lcdporto/warehouse-locator/hardware/warehouse-locator.kicad_sch

## KiCad design hardware/warehouse-locator.kicad_sch (2023-01-04, an earlier design)

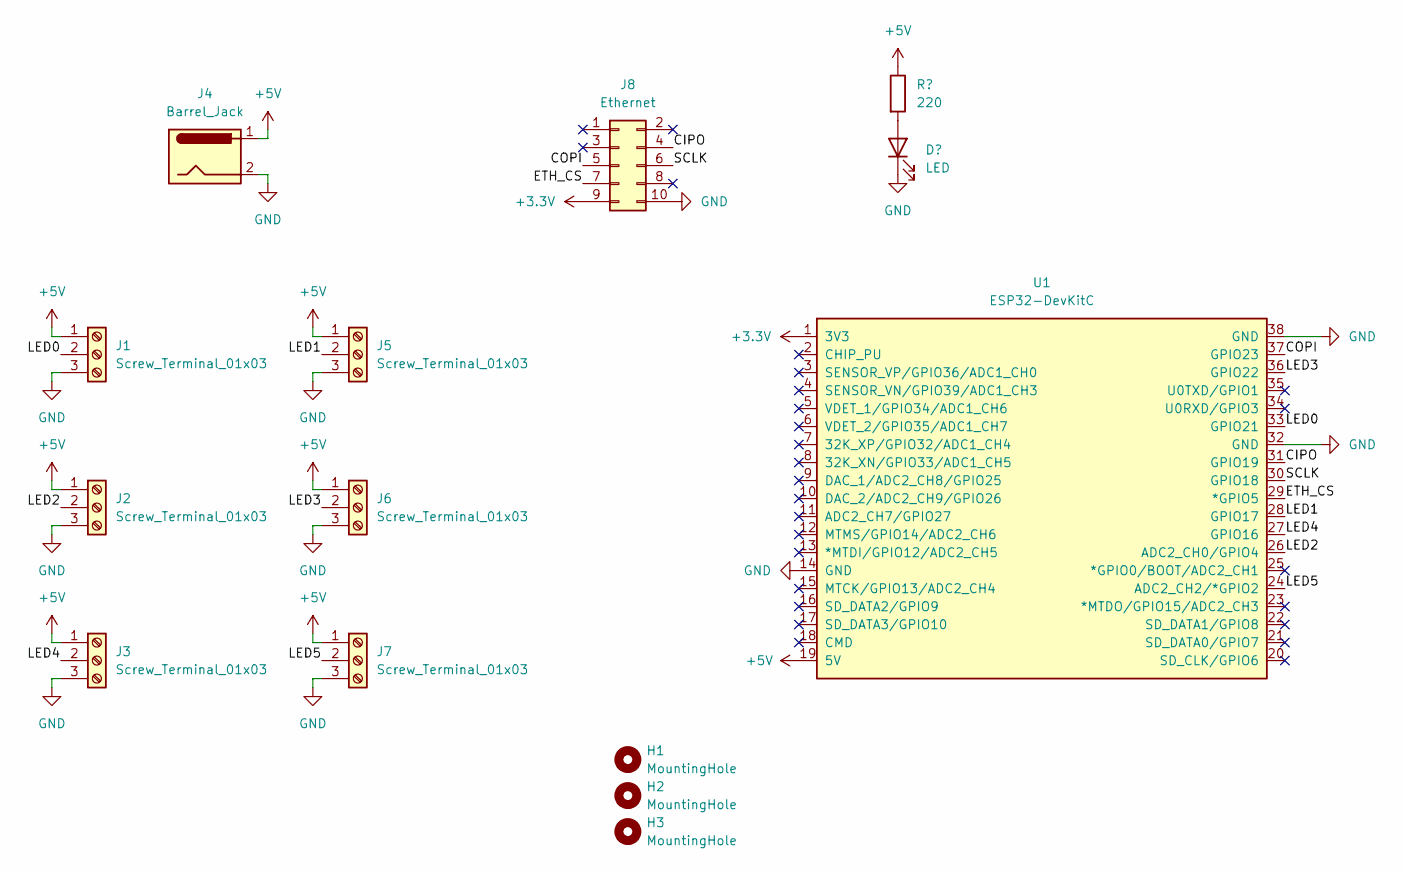
[picture p2: schematic warehouse-locator.kicad_sch]

Parts:
H1, H2, H3: MountingHole; MountingHole_3.2mm_M3_DIN965_Pad
J1, J2, J3, J5, J6, J7: Screw_Terminal_01x03; TerminalBlock_Phoenix_MKDS-1,5-3_1x03_P5.00mm_Horizontal
J4: Barrel_Jack; BarrelJack_Horizontal
J8: Ethernet; PinSocket_2x05_P2.54mm_Vertical
U1: ESP32-DevKitC

Connections:
+3.3V: J8.9
+5V: J1.1, J2.1, J3.1, J4.1, J5.1, J6.1, J7.1
CIPO: J8.4, U1.31 (GPIO19)
COPI: J8.5, U1.37 (GPIO23)
ETH_CS: J8.7, U1.29 (*GPIO5)
GND: J1.3, J2.3, J3.3, J4.2, J5.3, J6.3, J7.3, J8.10
LED0: J1.2, U1.33 (GPIO21)
LED1: J5.2, U1.28 (GPIO17)
LED2: J2.2, U1.26 (ADC2_CH0/GPIO4)
LED3: J6.2, U1.36 (GPIO22)
LED4: J3.2, U1.27 (GPIO16)
LED5: J7.2, U1.24 (ADC2_CH2/*GPIO2)
SCLK: J8.6, U1.30 (GPIO18)
